cdyn/kkClave/images/kkClave_12Vbreakout.jpg

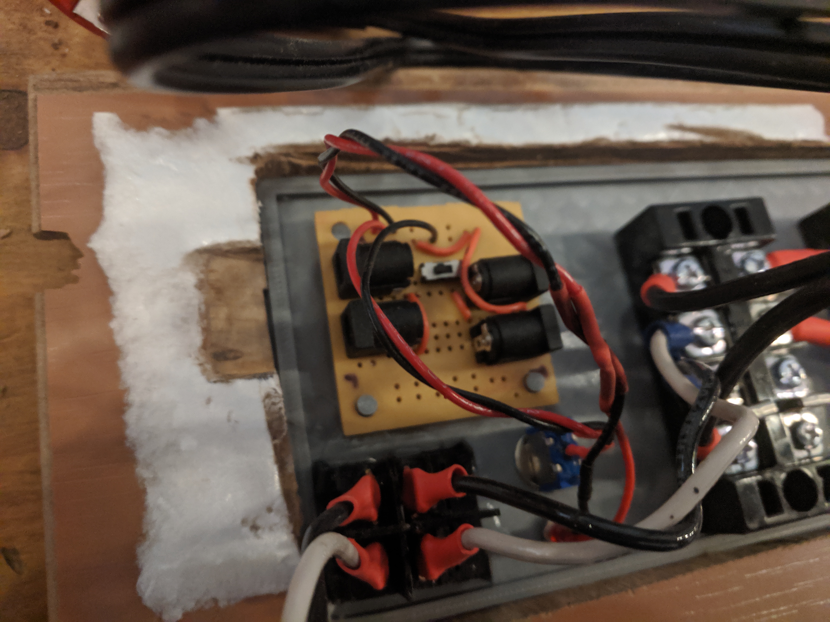
images/kkClave_12Vbreakout.jpg
