cdyn/kkClave/images/kkClave_fridgeTeardown.jpg

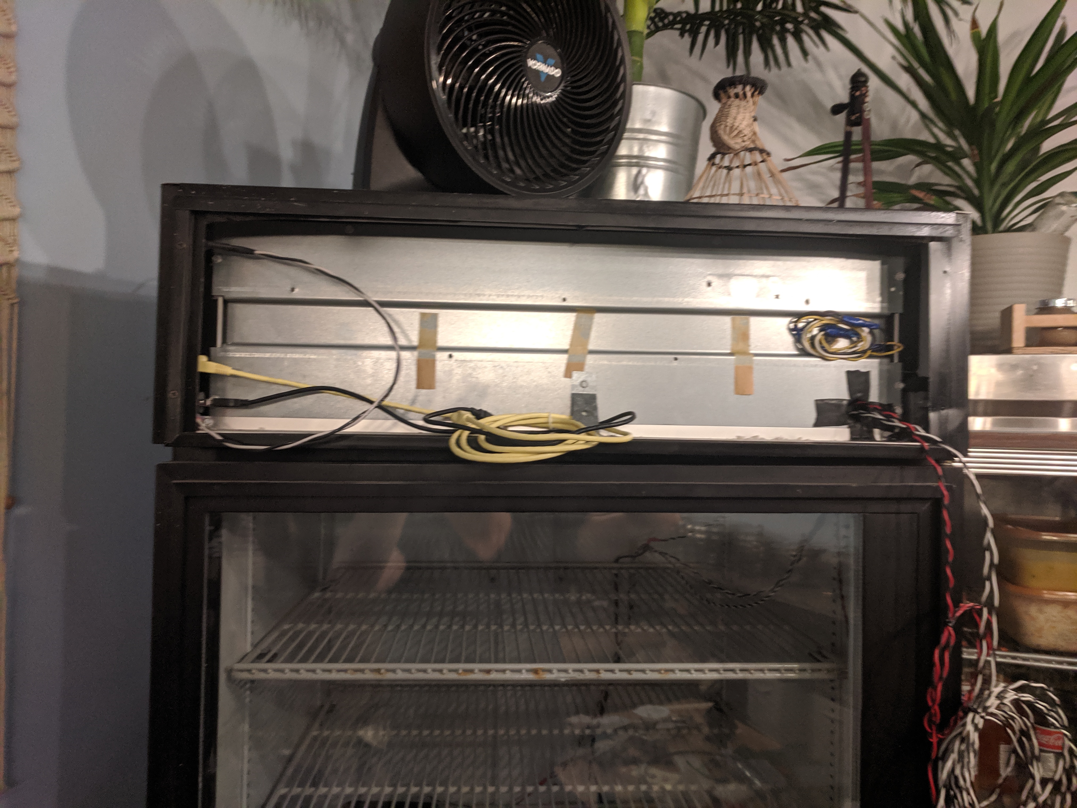
images/kkClave_fridgeTeardown.jpg
