cdyn/kkClave/images/kkClave_frontPanelFit.jpg

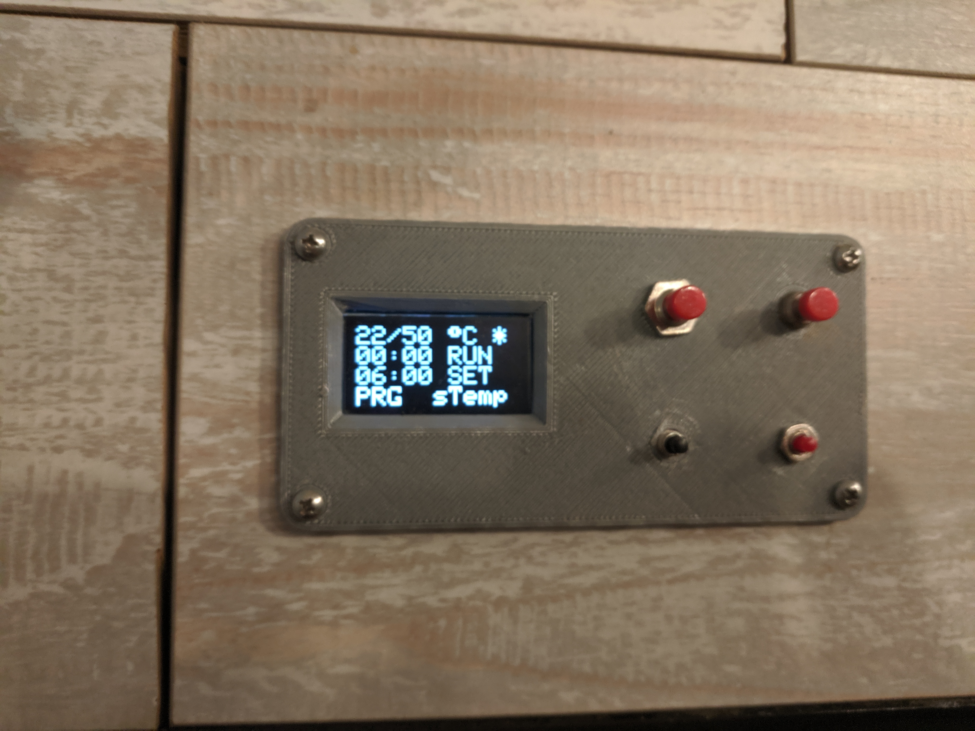
images/kkClave_frontPanelFit.jpg
