cdyn/kkClave/images/kkClave_ledStrip.jpg

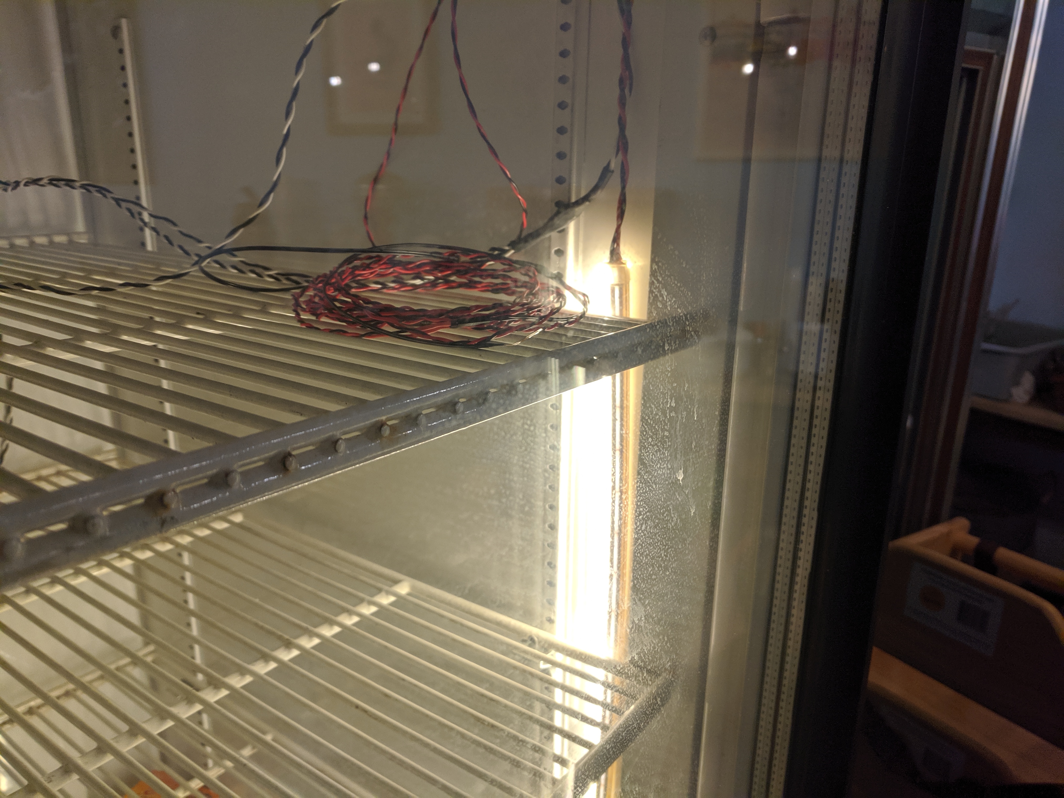
images/kkClave_ledStrip.jpg
