cdyn/kkClave/images/kkClave_logic1.jpg

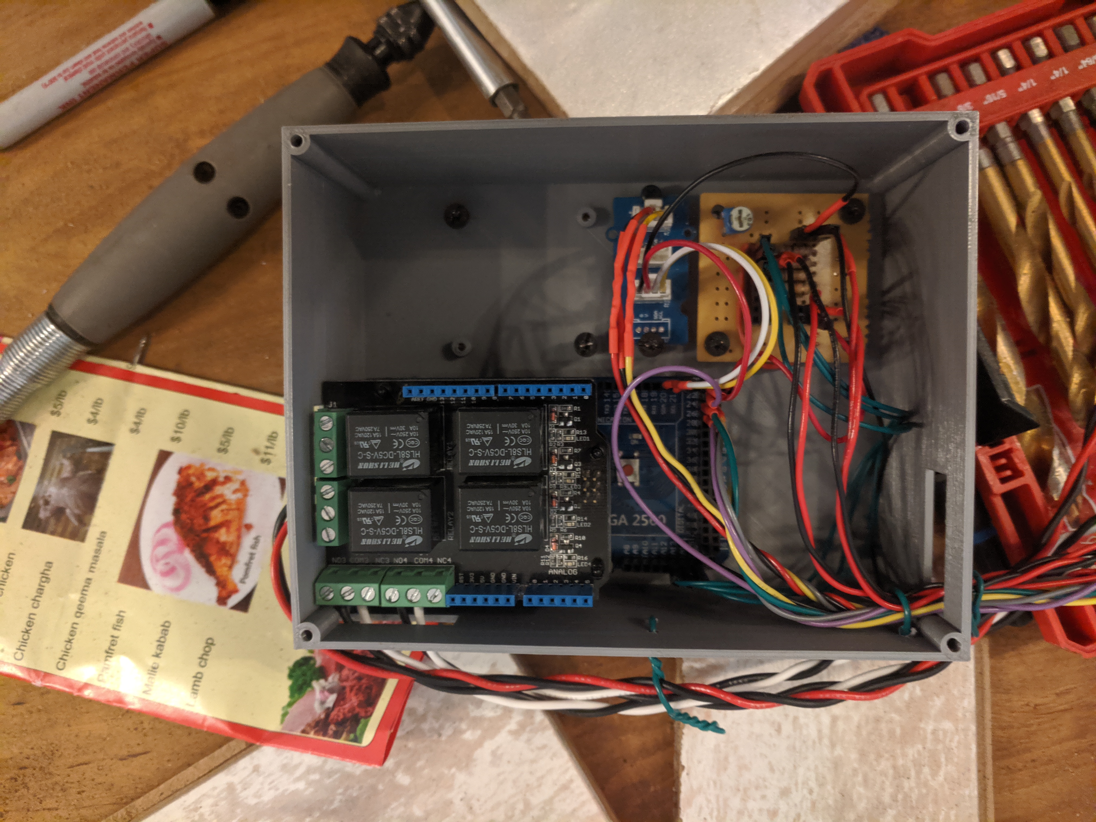
images/kkClave_logic1.jpg
