cdyn/kkClave/images/kkClave_logic2.jpg

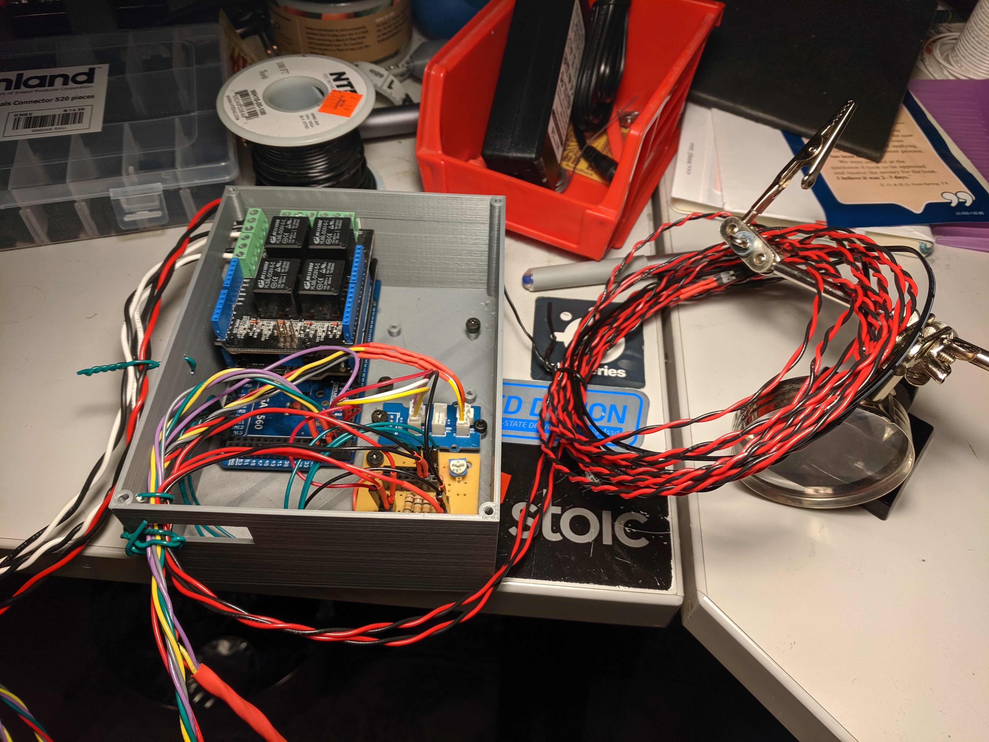
images/kkClave_logic2.jpg
