cdyn/kkClave/images/kkClave_logicFit.jpg

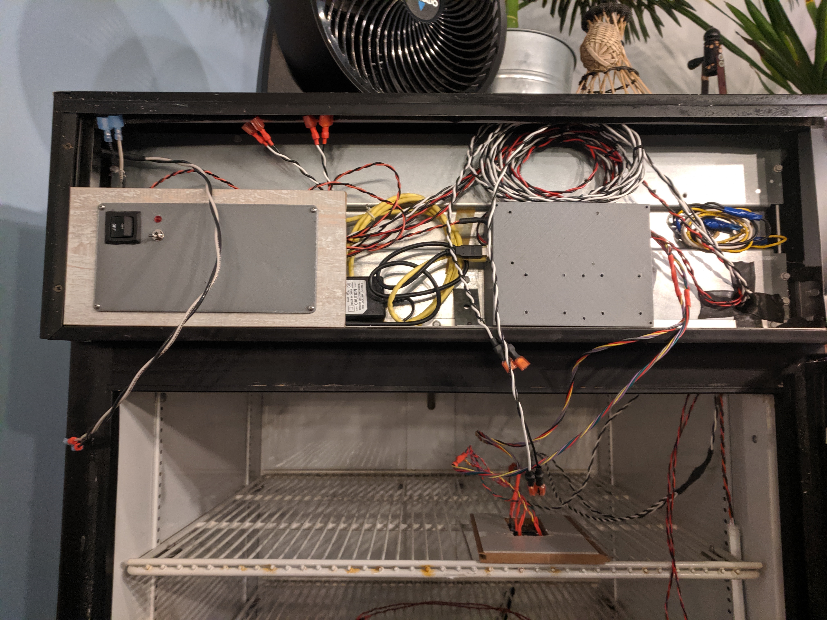
images/kkClave_logicFit.jpg
