cdyn/kkClave/images/kkClave_pwrPanelFit.jpg

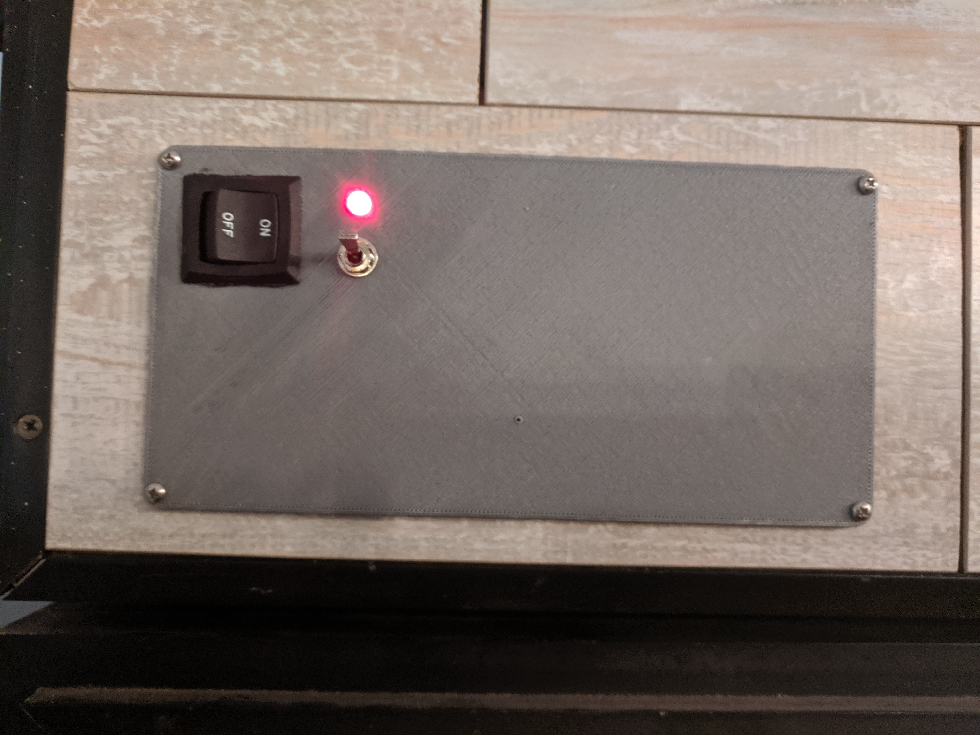
images/kkClave_pwrPanelFit.jpg
